kArmadi110/Gatherer3Dv2/docs/results/benchy.png

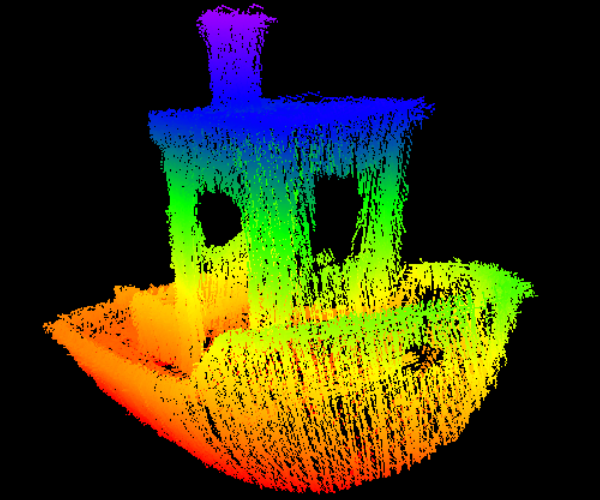
docs/results/benchy.png
