kArmadi110/Gatherer3Dv2/docs/results/bunny.png

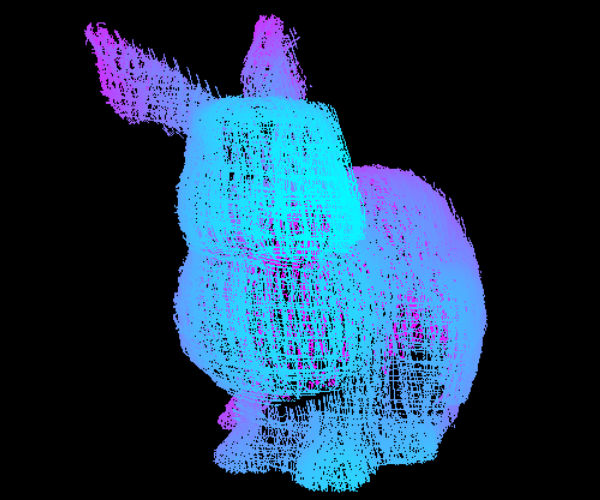
docs/results/bunny.png
